grodansparadis/pizero_wireless1/images/gerbers_pizero_w1_rev_a_gbl_small.png

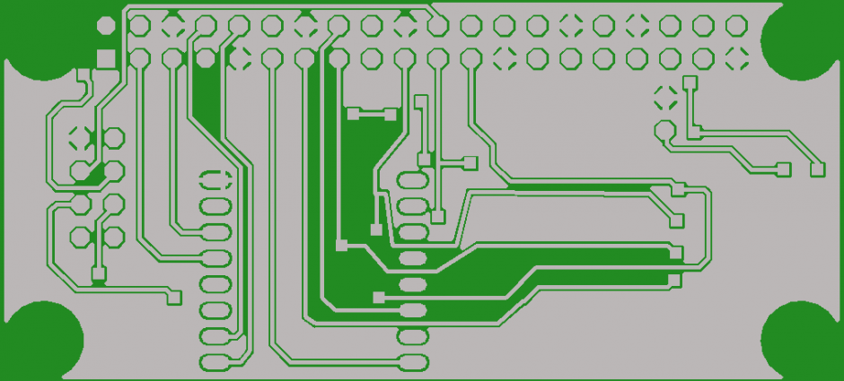
images/gerbers_pizero_w1_rev_a_gbl_small.png
