grodansparadis/pizero_wireless1/images/gerbers_pizero_w1_rev_a_txt_small.png

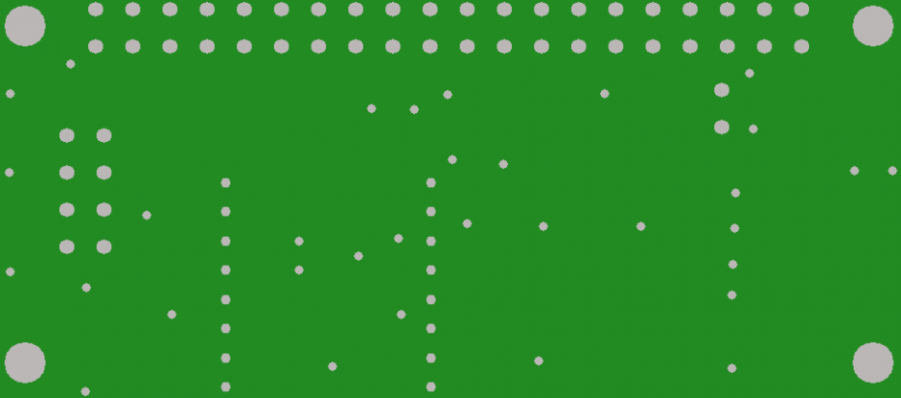
images/gerbers_pizero_w1_rev_a_txt_small.png
